spencerBlanchard/xx9TurbolaserBattery/print_files/sideTop_joystick_v02.stl

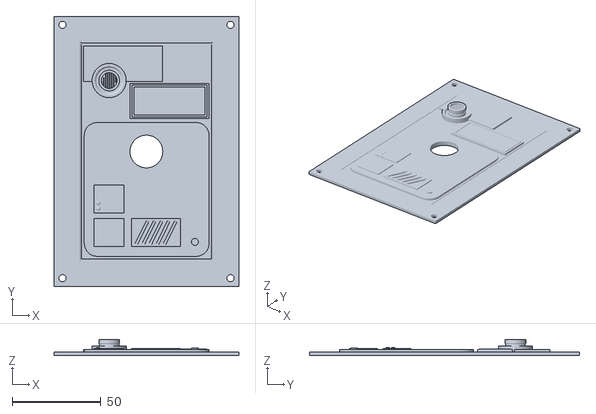
[picture p15: CAD file, 2026-09-20]
print_files/sideTop_joystick_v02.stl
104.3 x 152.3 x 9.10
