spencerBlanchard/xx9TurbolaserBattery/print_files/rod_v01.stl

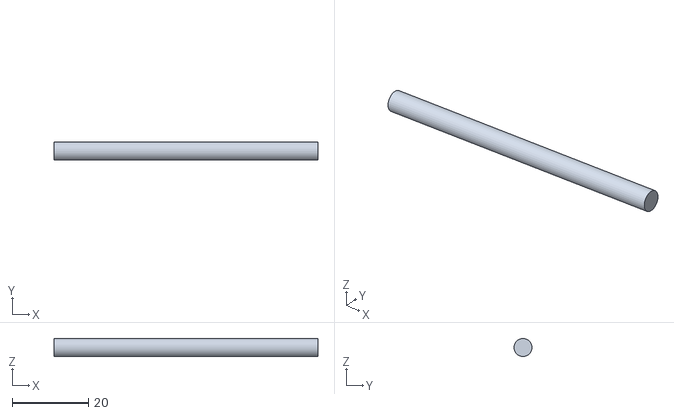
[picture p16: CAD file, 2026-09-20]
print_files/rod_v01.stl
69.2 x 4.74 x 4.74
