spencerBlanchard/xx9TurbolaserBattery/print_files/yawBottom_v02.stl

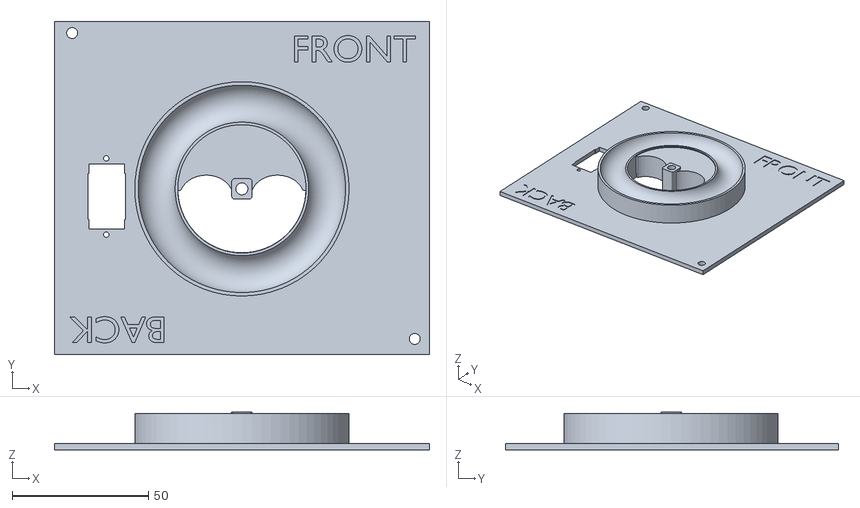
[picture p17: CAD file, 2026-09-20]
print_files/yawBottom_v02.stl
137.7 x 122.3 x 13.9
