spencerBlanchard/xx9TurbolaserBattery/print_files/gear_linearActuator_round_v01.stl

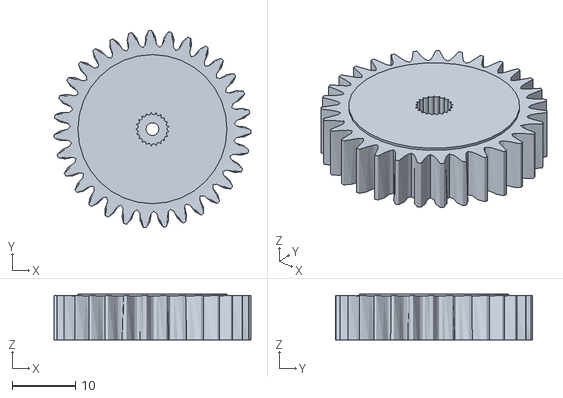
[picture p18: CAD file, 2026-09-20]
print_files/gear_linearActuator_round_v01.stl
31.1 x 31.1 x 7.22
