spencerBlanchard/xx9TurbolaserBattery/xx9turbolaser/xwing_sprites.h

#ifndef XWING_SPRITES_H
#define XWING_SPRITES_H

#include <Arduino.h>

const int XWING_WIDTH = 23;
const int XWING_HEIGHT = 15;

const uint16_t XWING_NORMAL_PIXELS[XWING_WIDTH * XWING_HEIGHT] PROGMEM = {
  0xFFFF, 0xFFFF, 0xFFFF, 0xFFFF, 0xFFFF, 0xFFFF, 0xFFFF, 0xFFFF, 0xFFFF, 0xFFFF, 0xFFFF, 0xFFFF,
  0xFFFF, 0xFFFF, 0xFFFF, 0xFFFF, 0xFFFF, 0xFFFF, 0xFFFF, 0xFFFF, 0xFFFF, 0xFFFF, 0xFFFF, 0xFFFF,
  0x8800, 0xF79E, 0x0000, 0x0000, 0xFFFF, 0xFFFF, 0xFFFF, 0xFFFF, 0xFFFF, 0xFFFF, 0xFFFF, 0xFFFF,
  0xFFFF, 0xFFFF, 0xFFFF, 0xFFFF, 0xFFFF, 0xFFFF, 0x0000, 0xF79E, 0x8800, 0xFFFF, 0xFFFF, 0xF79E,
  0xF79E, 0xF79E, 0xF79E, 0xFFFF, 0xFFFF, 0xFFFF, 0xFFFF, 0xFFFF, 0xFFFF, 0xFFFF, 0xFFFF, 0xFFFF,
  0xFFFF, 0xFFFF, 0xFFFF, 0xFFFF, 0xFFFF, 0xF79E, 0xF79E, 0xF79E, 0xFFFF, 0xFFFF, 0x8800, 0x0000,
  0xF79E, 0xFFFF, 0xFFFF, 0xFFFF, 0xBDF7, 0xBDF7, 0x0000, 0x0000, 0xFFFF, 0xFFFF, 0x0000, 0xBDF7,
  0xBDF7, 0xBDF7, 0xFFFF, 0xFFFF, 0xF79E, 0x0000, 0x8800, 0xFFFF, 0xFFFF, 0xF79E, 0xF79E, 0x0000,
  0xF79E, 0xFFFF, 0xBDF7, 0x2945, 0x2945, 0xBDF7, 0x2800, 0xF79E, 0x2800, 0xBDF7, 0x2945, 0x2945,
  0xBDF7, 0xFFFF, 0xF79E, 0xF79E, 0xF79E, 0xF79E, 0xFFFF, 0xFFFF, 0xFFFF, 0x0000, 0x0000, 0xFFFF,
  0xFFFF, 0xBDF7, 0x2945, 0x2945, 0xBDF7, 0x8535, 0x8535, 0x8535, 0xBDF7, 0x2945, 0x2945, 0xBDF7,
  0xBDF7, 0xFFFF, 0xFFFF, 0x0000, 0x0000, 0xFFFF, 0xFFFF, 0xFFFF, 0xFFFF, 0xFFFF, 0xF79E, 0xFFFF,
  0xBDF7, 0xBDF7, 0xBDF7, 0x8535, 0x8535, 0x5C11, 0x8535, 0x8535, 0xBDF7, 0xBDF7, 0x2945, 0xBDF7,
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
  0x069F, 0x069F, 0xF79E, 0xBDF7, 0xBDF7, 0x069F, 0x069F, 0xBDF7, 0xFFFF, 0x069F, 0x069F, 0x069F,
  0x069F, 0xF79E, 0xF79E, 0xF79E, 0x069F, 0x069F, 0x069F, 0x069F, 0x069F, 0x069F, 0x069F, 0x471F,
  0x069F, 0x069F, 0x069F, 0x069F, 0x069F, 0x069F, 0x069F, 0xF79E, 0xF79E, 0xF79E, 0x069F, 0x069F,
  0xF800, 0xF79E, 0x069F, 0x069F, 0x873F, 0x873F, 0x873F, 0x471F, 0x471F, 0x471F, 0x873F, 0x471F,
  0x471F, 0x471F, 0x873F, 0x873F, 0x873F, 0x069F, 0x069F, 0xF79E, 0xF800, 0x069F, 0x069F, 0x069F,
  0x069F, 0x069F, 0x873F, 0xFFFF, 0xFFFF, 0xFFFF, 0xFFFF, 0xFFFF, 0xFFFF, 0xFFFF, 0xFFFF, 0xFFFF,
  0xFFFF, 0xFFFF, 0xFFFF, 0xFFFF, 0x873F, 0x069F, 0x069F, 0x069F, 0x069F,
};

const uint8_t XWING_SHIELD_MASK[((XWING_WIDTH + 7) / 8) * XWING_HEIGHT] PROGMEM = {
  0xF8, 0x00, 0x3E, 0xFF, 0xFF, 0xFE, 0xFF, 0xFF, 0xFE, 0xFF, 0xFF, 0xFE,
  0x7F, 0xFF, 0xFC, 0x7F, 0xFF, 0xFC, 0x3F, 0xFF, 0xF8, 0x1F, 0xFF, 0xF0,
  0x3F, 0xFF, 0xF8, 0x7F, 0xFF, 0xFC, 0x7F, 0xFF, 0xFC, 0xFF, 0xFF, 0xFE,
  0xFF, 0xFF, 0xFE, 0xFF, 0xFF, 0xFE, 0xF8, 0x00, 0x3E,
};

#endif  // XWING_SPRITES_H
